nofitnessforpurpose/TopSlotDataPack/images/TSDP03.jpg

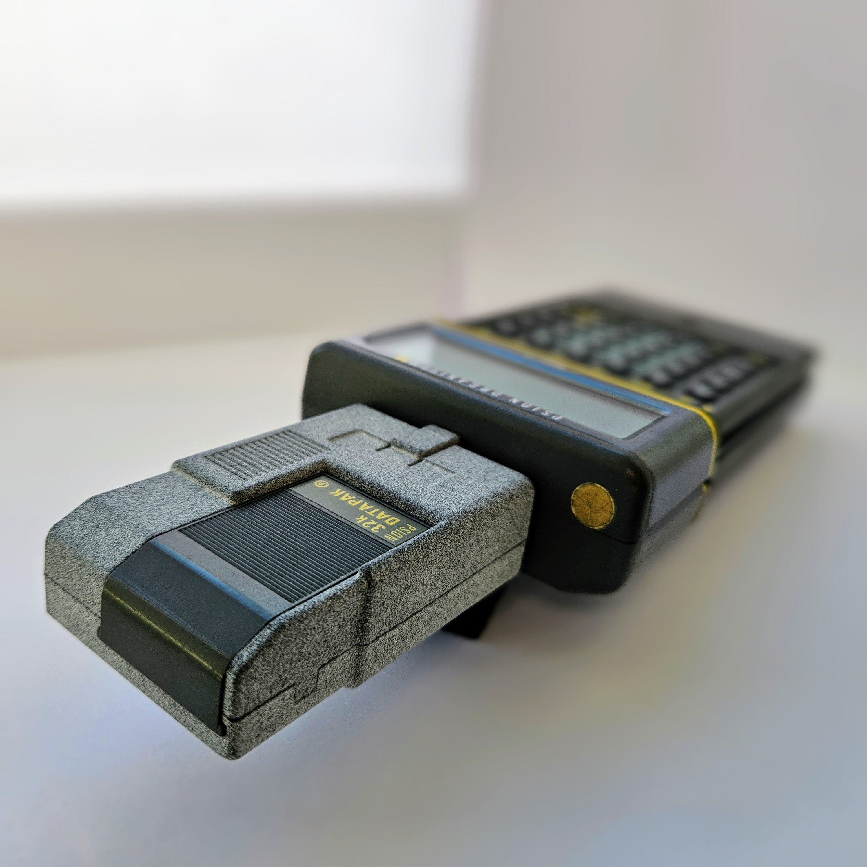
images/TSDP03.jpg
