nofitnessforpurpose/TopSlotDataPack/images/TSDP-05.jpg

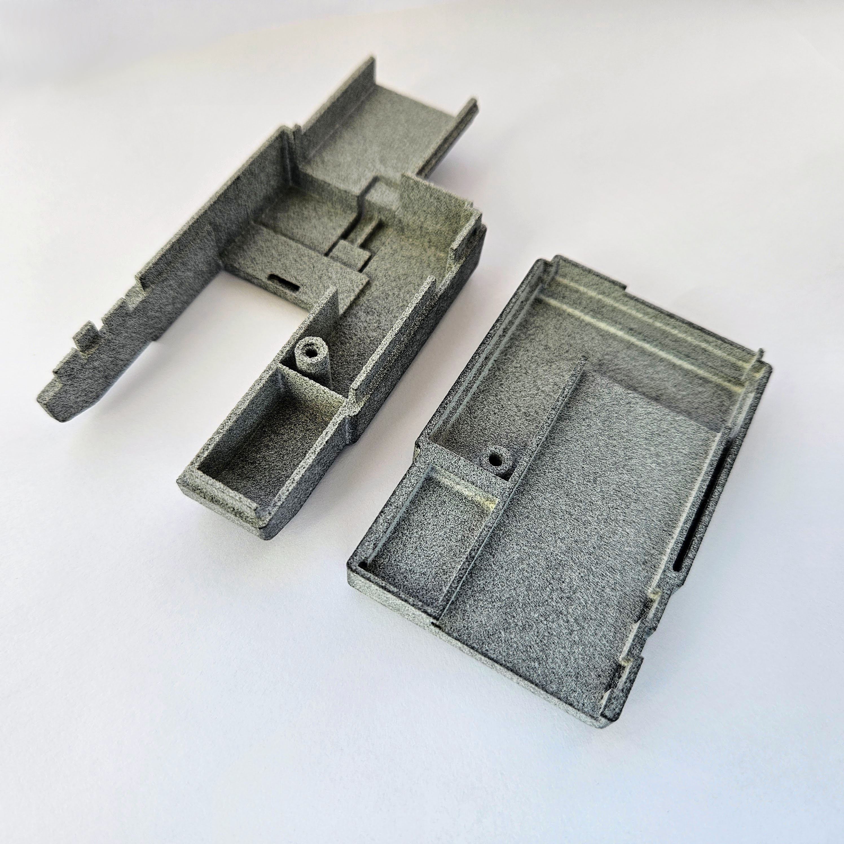
images/TSDP-05.jpg
