nofitnessforpurpose/TopSlotDataPack/images/TSDP-09.jpg

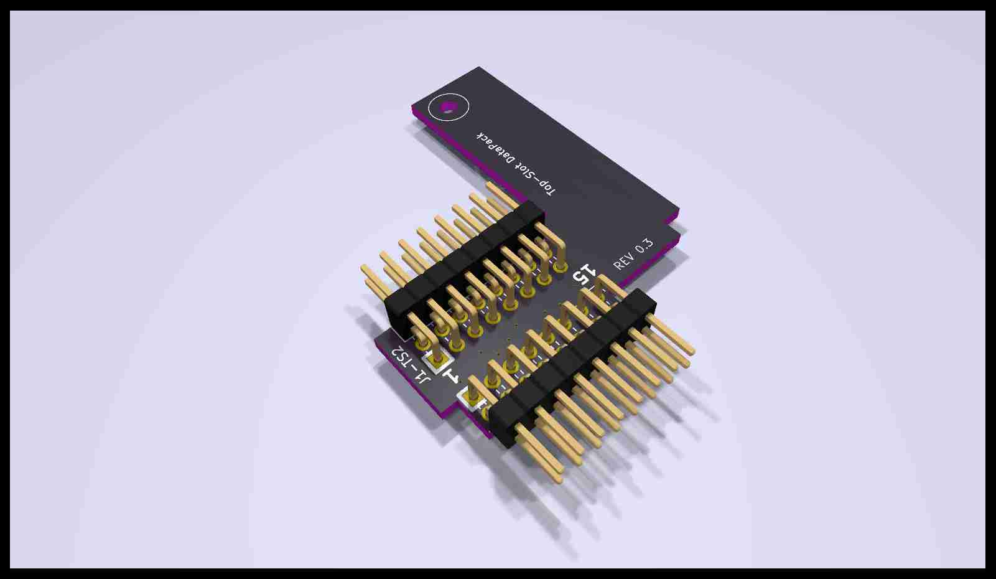
images/TSDP-09.jpg
